krynentechnology/sr2cb/rtl/sr2cb_s_tb.sv

/**
 *  Copyright (C) 2024, Kees Krijnen.
 *
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
 *  License: GPL, v3, as defined and found on www.gnu.org,
 *           https://www.gnu.org/licenses/gpl-3.0.html
 *
 *  Description:
 *
 *  Documents the SR2CB specification by simulation of the SR2CB protocol. The
 *  simulation is setup by SR2CB ring slave nodes clockwise and counterclockwise
 *  byte transfers initiated by a simulated master node (test bench).
 */

`resetall
`timescale 1ns / 1ps
`default_nettype none

// Dependencies:
// `include "../sr2cb_m_phy_pre.v"
// `include "../sr2cb_s.v"
`include "sr2cb_def.v"

/*============================================================================*/
module sr2cb_s_tb;
/*============================================================================*/
localparam NR_CHANNELS = 4;
localparam CHW = $clog2( NR_CHANNELS );

reg        clk = 0;
reg        rst_n = 0;
wire       rx0m_clk;
wire [7:0] rx0m_d;
wire       rx0m_dv;
wire       rx1m_clk;
wire [7:0] rx1m_d;
wire       rx1m_dv;
reg        tx0m_clk = 0;
reg  [7:0] tx0m_d = 0;
reg        tx0m_dv = 0;
wire [7:0] phy_pre_0_d;
wire       phy_pre_0_dv;
wire       phy_pre_0_dr;
reg        tx1m_clk = 0;
reg  [7:0] tx1m_d = 0;
reg        tx1m_dv = 0;
wire [7:0] phy_pre_1_d;
wire       phy_pre_1_dv;
wire       phy_pre_1_dr;
wire [7:0] tx0s0_d;
wire       tx0s0_dv;
wire       tx1s0_clk;
wire [7:0] tx1s0_d;
wire       tx1s0_dv;
wire       tx0s1_clk;
wire [7:0] tx0s1_d;
wire       tx0s1_dv;
wire       tx1s1_clk;
wire [7:0] tx1s1_d;
wire       tx1s1_dv;
wire       tx0s2_clk;
wire [7:0] tx0s2_d;
wire       tx0s2_dv;
wire [7:0] tx1s2_d;
wire       tx1s2_dv;
/*-------------------*/
wire [7:0] rx0s0_ch_d;
wire       rx0s0_ch_dv;
wire       rx0s0_ch_dr;
wire [7:0] tx0s0_ch_d;
wire [CHW-1:0] rx0s0_tx0_ch;
reg  [7:0] rx1s0_ch_d = 0;
reg        rx1s0_ch_dv = 0;
wire       rx1s0_ch_dr;
wire [7:0] tx1s0_ch_d;
wire [CHW-1:0] rx1s0_tx1_ch;
reg  [7:0] rx0s2_ch_d = 0;
reg        rx0s2_ch_dv = 0;
wire       rx0s2_ch_dr;
wire [7:0] tx0s2_ch_d;
wire [CHW-1:0] rx0s2_tx0_ch;
wire [7:0] rx1s2_ch_d;
wire       rx1s2_ch_dv;
wire       rx1s2_ch_dr;
wire [7:0] tx1s2_ch_d;
wire [CHW-1:0] rx1s2_tx1_ch;
/*---------------------------*/
reg   [7:0] rx0_d_count = 0;
reg   [7:0] rx1_d_count = 0;
wire [67:0] rx0s0_rt_clk_count;
wire [67:0] rx1s0_rt_clk_count;
wire [67:0] rx0s1_rt_clk_count;
wire [67:0] rx1s1_rt_clk_count;
wire [67:0] rx0s2_rt_clk_count;
wire [67:0] rx1s2_rt_clk_count;
/*---------------------------*/
reg [7:0] tx0p_d = 0;
reg       tx0p_dv = 0;
reg [7:0] tx0m_d_i = 0;
reg       tx0m_dv_i = 0;
reg [7:0] tx0m_d_ii = 0;
reg       tx0m_dv_ii = 0;
/*---------------------------*/
reg [7:0] tx0s1_d_i = 0;
reg       tx0s1_dv_i = 0;
/*---------------------------*/
reg [7:0] tx0s2_d_i = 0;
reg       tx0s2_dv_i = 0;
/*---------------------------*/
reg [7:0] tx1p_d = 0;
reg       tx1p_dv = 0;
reg [7:0] tx1m_d_i = 0;
reg       tx1m_dv_i = 0;
reg [7:0] tx1m_d_ii = 0;
reg       tx1m_dv_ii = 0;

/*=============================================================================/
RING         | SLV0    |  | SLV1    |         | SLV8190 |  | SLV8191 |
|  +------+  +---------+  +---------+         +---------+  +---------+  +------+
|  |MASTER|  | NP 8191 |  | NP 8190 |         | NP 1    |  | NP 0    |  |MASTER|
CCW|  RX0 |<-| TX0 RX1 |<-| TX0 RX1 |<- - - <-| TX0 RX1 |<-| TX0 RX1 |<-| TX1  |
|  |      |  | NP 0    |    NP 1    |         | NP 8190 |    NP 8191 |  |      |
CW |  TX0 |->| RX0 TX1 |->| RX0 TX1 |->- - ->-| RX0 TX1 |->| RX0 TX1 |->| RX1  |
   +------+  +---------+  +---------+         +---------+  +---------+  +------+
/=============================================================================*/

/*============================================================================*/
sr2cb_m_phy_pre phy_pre_0(
/*============================================================================*/
    .clk(tx0m_clk),
    .rst_n(rst_n),
    .rx_d(tx0m_d),
    .rx_dv(tx0m_dv),
    .rx_dr(phy_pre_0_dr),
    .tx_d(phy_pre_0_d),
    .tx_dv(phy_pre_0_dv)
);

/*============================================================================*/
sr2cb_s slv_node_0(
/*============================================================================*/
    .clk(clk),
    .rst_n(rst_n),
    .rx0_clk(tx0m_clk),
    .rx0_d(tx0m_d_ii),
    .rx0_dv(tx0m_dv_ii),
    .rx0_err(1'b0),
    .tx0_clk(rx0m_clk),
    .tx0_d(tx0s0_d),
    .tx0_dv(tx0s0_dv),
    .tx0_dr(1'b1),
    .tx0_err(),
    .rx1_clk(tx0s1_clk),
    .rx1_d(tx0s1_d_i),
    .rx1_dv(tx0s1_dv_i),
    .rx1_err(1'b0),
    .tx1_clk(tx1s0_clk),
    .tx1_d(tx1s0_d),
    .tx1_dv(tx1s0_dv),
    .tx1_dr(1'b1),
    .tx1_err(),
    .rx0_ch_d(rx0s0_ch_d),
    .rx0_ch_dv(rx0s0_ch_dv),
    .rx0_ch_dr(rx0s0_ch_dr),
    .tx0_ch_d(tx0s0_ch_d),
    .rx0_tx0_ch(rx0s0_tx0_ch),
    .rx1_ch_d(rx1s0_ch_d),
    .rx1_ch_dv(rx1s0_ch_dv),
    .rx1_ch_dr(rx1s0_ch_dr),
    .tx1_ch_d(tx1s0_ch_d),
    .rx1_tx1_ch(rx1s0_tx1_ch),
    .rx0_node_pos(),
    .rx0_c_s(),
    .rx0_status(),
    .rx0_delay(),
    .rx0_rt_clk_count(rx0s0_rt_clk_count),
    .rx0_clk_adjust_fast(),
    .rx1_node_pos(),
    .rx1_c_s(),
    .rx1_status(),
    .rx1_delay(),
    .rx1_rt_clk_count(rx1s0_rt_clk_count),
    .rx1_clk_adjust_fast(),
    .clk_en(),
    .dv_en()
);

defparam slv_node_0.NR_CHANNELS = NR_CHANNELS;

/*============================================================================*/
always @( posedge tx0m_clk ) // Two clock cycle interface RX signal delay
/*============================================================================*/
begin
    tx0p_d     <= 0;
    tx0p_dv    <= 0;
    tx0m_d_i   <= 0;
    tx0m_dv_i  <= 0;
    tx0m_d_ii  <= 0;
    tx0m_dv_ii <= 0;
    if ( rst_n ) begin // Extra clock cycle, tx0m_dv starts at negedge!
        tx0m_d_i   <= ( phy_pre_0_d & { 8{ phy_pre_0_dv }} ) | ( tx0p_d & { 8{ tx0p_dv }} );
        tx0m_dv_i  <= phy_pre_0_dv | tx0p_dv;
        tx0m_d_ii  <= tx0m_d_i;
        tx0m_dv_ii <= tx0m_dv_i;
    end
end // tx0m_clk

reg [7:0] tx0s0_d_i = 0;
reg       tx0s0_dv_i = 0;
/*============================================================================*/
always @( posedge rx0m_clk ) // One clock cycle interface RX signal delay
/*============================================================================*/
begin
    tx0s0_d_i  <= 0;
    tx0s0_dv_i <= 0;
    if ( rst_n ) begin
        tx0s0_d_i  <= tx0s0_d;
        tx0s0_dv_i <= tx0s0_dv;
    end
end // rx0m_clk

assign rx0m_d  = tx0s0_d_i;
assign rx0m_dv = tx0s0_dv_i;

reg [7:0] tx1s0_d_i = 0;
reg       tx1s0_dv_i = 0;
/*============================================================================*/
always @( posedge tx1s0_clk ) // One clock cycle interface RX signal delay
/*============================================================================*/
begin
    tx1s0_d_i  <= 0;
    tx1s0_dv_i <= 0;
    if ( rst_n ) begin
        tx1s0_d_i  <= tx1s0_d;
        tx1s0_dv_i <= tx1s0_dv;
    end
end // tx1s0_clk

/*============================================================================*/
sr2cb_s slv_node_1(
/*============================================================================*/
    .clk(clk),
    .rst_n(rst_n),
    .rx0_clk(tx1s0_clk),
    .rx0_d(tx1s0_d_i),
    .rx0_dv(tx1s0_dv_i),
    .rx0_err(1'b0),
    .tx0_clk(tx0s1_clk),
    .tx0_d(tx0s1_d),
    .tx0_dv(tx0s1_dv),
    .tx0_dr(1'b1),
    .tx0_err(),
    .rx1_clk(tx0s2_clk),
    .rx1_d(tx0s2_d_i),
    .rx1_dv(tx0s2_dv_i),
    .rx1_err(1'b0),
    .tx1_clk(tx1s1_clk),
    .tx1_d(tx1s1_d),
    .tx1_dv(tx1s1_dv),
    .tx1_dr(1'b1),
    .tx1_err(),
    .rx0_ch_d(8'd0),
    .rx0_ch_dv(1'b0),
    .rx0_ch_dr(),
    .tx0_ch_d(),
    .rx0_tx0_ch(),
    .rx1_ch_d(8'd0),
    .rx1_ch_dv(1'b0),
    .rx0_ch_dr(),
    .tx1_ch_d(),
    .rx1_tx1_ch(),
    .rx0_node_pos(),
    .rx0_c_s(),
    .rx0_status(),
    .rx0_delay(),
    .rx0_rt_clk_count(rx0s1_rt_clk_count),
    .rx0_clk_adjust_fast(),
    .rx1_node_pos(),
    .rx1_c_s(),
    .rx1_status(),
    .rx1_delay(),
    .rx1_rt_clk_count(rx1s1_rt_clk_count),
    .rx1_clk_adjust_fast()
);

defparam slv_node_1.NR_CHANNELS = NR_CHANNELS;

/*============================================================================*/
always @( posedge tx0s1_clk ) // One clock cycle interface RX signal delay
/*============================================================================*/
begin
    tx0s1_d_i  <= 0;
    tx0s1_dv_i <= 0;
    if ( rst_n ) begin
        tx0s1_d_i  <= tx0s1_d;
        tx0s1_dv_i <= tx0s1_dv;
    end
end // tx0s1_clk

reg [7:0] tx1s1_d_i = 0;
reg       tx1s1_dv_i = 0;
/*============================================================================*/
always @( posedge tx1s1_clk ) // One clock cycle interface RX signal delay
/*============================================================================*/
begin
    tx1s1_d_i  <= 0;
    tx1s1_dv_i <= 0;
    if ( rst_n ) begin
        tx1s1_d_i  <= tx1s1_d;
        tx1s1_dv_i <= tx1s1_dv;
    end
end // tx1s1_clk

/*============================================================================*/
sr2cb_s slv_node_2(
/*============================================================================*/
    .clk(clk),
    .rst_n(rst_n),
    .rx0_clk(tx1s1_clk),
    .rx0_d(tx1s1_d_i),
    .rx0_dv(tx1s1_dv_i),
    .rx0_err(1'b0),
    .tx0_clk(tx0s2_clk),
    .tx0_d(tx0s2_d),
    .tx0_dv(tx0s2_dv),
    .tx0_dr(1'b1),
    .tx0_err(),
    .rx1_clk(tx1m_clk),
    .rx1_d(tx1m_d_ii),
    .rx1_dv(tx1m_dv_ii),
    .rx1_err(1'b0),
    .tx1_clk(rx1m_clk),
    .tx1_d(tx1s2_d),
    .tx1_dv(tx1s2_dv),
    .tx1_dr(1'b1),
    .tx1_err(),
    .rx0_ch_d(rx0s2_ch_d),
    .rx0_ch_dv(rx0s2_ch_dv),
    .rx0_ch_dr(rx0s2_ch_dr),
    .tx0_ch_d(tx0s2_ch_d),
    .rx0_tx0_ch(rx0s2_tx0_ch),
    .rx1_ch_d(rx1s2_ch_d),
    .rx1_ch_dv(rx1s2_ch_dv),
    .rx1_ch_dr(rx1s2_ch_dr),
    .tx1_ch_d(tx1s2_ch_d),
    .rx1_tx1_ch(rx1s2_tx1_ch),
    .rx0_node_pos(),
    .rx0_c_s(),
    .rx0_status(),
    .rx0_delay(),
    .rx0_rt_clk_count(rx0s2_rt_clk_count),
    .rx0_clk_adjust_fast(),
    .rx1_node_pos(),
    .rx1_c_s(),
    .rx1_status(),
    .rx1_delay(),
    .rx1_rt_clk_count(rx1s2_rt_clk_count),
    .rx1_clk_adjust_fast()
);

defparam slv_node_2.NR_CHANNELS = NR_CHANNELS;

/*============================================================================*/
always @( posedge tx0s2_clk ) // One clock cycle interface RX signal delay
/*============================================================================*/
begin
    tx0s2_d_i  <= 0;
    tx0s2_dv_i <= 0;
    if ( rst_n ) begin
        tx0s2_d_i  <= tx0s2_d;
        tx0s2_dv_i <= tx0s2_dv;
    end
end // tx0s2_clk

/*============================================================================*/
always @( posedge tx1m_clk ) // Two clock cycle interface RX signal delay
/*============================================================================*/
begin
    tx1p_d     <= 0;
    tx1p_dv    <= 0;
    tx1m_d_i   <= 0;
    tx1m_dv_i  <= 0;
    tx1m_d_ii  <= 0;
    tx1m_dv_ii <= 0;
    if ( rst_n ) begin // Extra clock cycle, tx1m_dv starts at negedge!
        tx1m_d_i   <= ( phy_pre_1_d & { 8{ phy_pre_1_dv }} ) | ( tx1p_d & { 8{ tx1p_dv }} );
        tx1m_dv_i  <= phy_pre_1_dv | tx1p_dv;
        tx1m_d_ii  <= tx1m_d_i;
        tx1m_dv_ii <= tx1m_dv_i;
    end
end // tx1m_clk

/*============================================================================*/
sr2cb_m_phy_pre phy_pre_1(
/*============================================================================*/
    .clk(tx1m_clk),
    .rst_n(rst_n),
    .rx_d(tx1m_d),
    .rx_dv(tx1m_dv),
    .rx_dr(phy_pre_1_dr),
    .tx_d(phy_pre_1_d),
    .tx_dv(phy_pre_1_dv)
);

reg [7:0] tx1s2_d_i = 0;
reg       tx1s2_dv_i = 0;

/*============================================================================*/
always @( posedge rx1m_clk ) // One clock cycle interface RX signal delay
/*============================================================================*/
begin
    tx1s2_d_i  <= 0;
    tx1s2_dv_i <= 0;
    if ( rst_n ) begin
        tx1s2_d_i  <= tx1s2_d;
        tx1s2_dv_i <= tx1s2_dv;
    end
end // rx1m_clk

assign rx1m_d  = tx1s2_d_i;
assign rx1m_dv = tx1s2_dv_i;

reg [12:0] node_pos[0:1];
reg [12:0] node_pos_rp[0:1]; // The node positions of returned packets

/*============================================================================*/
task send_r0_byte( input [7:0] byte_in, input set_parity );
/*============================================================================*/
begin
    wait ( tx0m_clk ) @( negedge tx0m_clk );
    tx0m_d[6:0] = byte_in[6:0];
    tx0m_d[7]   = set_parity ? ~( ^byte_in[6:0] ) : byte_in[7];
    tx0m_dv = 1;
end
endtask // send_r0_byte

/*============================================================================*/
task send_r1_byte( input [7:0] byte_in, input set_parity );
/*============================================================================*/
begin
    wait ( tx1m_clk ) @( negedge tx1m_clk );
    tx1m_d[6:0] = byte_in[6:0];
    tx1m_d[7]   = set_parity ? ~( ^byte_in[6:0] ) : byte_in[7];
    tx1m_dv = 1;
end
endtask // send_r1_byte

/*============================================================================*/
task send_r0_command( input [12:0] cmd );
/*============================================================================*/
begin
    wait ( phy_pre_0_dr );
    send_r0_byte( {1'b0, node_pos[0][6:0]}, 1 );
    send_r0_byte( {1'b0, `CW_RDIR, node_pos[0][12:7]}, 1 );
    send_r0_byte( {1'b0, cmd[6:0]}, 1 );
    send_r0_byte( {1'b0, 1'b1, cmd[12:7]}, 1 ); // Set command bit
end
endtask // send_r0_command

/*============================================================================*/
task send_r1_command( input [12:0] cmd );
/*============================================================================*/
begin
    wait ( phy_pre_1_dr );
    send_r1_byte( {1'b0, node_pos[1][6:0]}, 1 );
    send_r1_byte( {1'b0, `CCW_RDIR, node_pos[1][12:7]}, 1 );
    send_r1_byte( {1'b0, cmd[6:0]}, 1 );
    send_r1_byte( {1'b0, 1'b1, cmd[12:7]}, 1 ); // Set command bit
end
endtask // send_r1_command

/*============================================================================*/
task send_r0_status( input [12:0] status );
/*============================================================================*/
begin
    wait ( phy_pre_0_dr );
    send_r0_byte( {1'b0, node_pos[0][6:0]}, 1 );
    send_r0_byte( {1'b0, `CW_RDIR, node_pos[0][12:7]}, 1 );
    send_r0_byte( {1'b0, status[6:0]}, 1 );
    send_r0_byte( {1'b0, 1'b0, status[12:7]}, 1 ); // Reset status bit
end
endtask // send_r0_status

/*============================================================================*/
task send_r1_status( input [12:0] status );
/*============================================================================*/
begin
    wait ( phy_pre_1_dr );
    send_r1_byte( {1'b0, node_pos[1][6:0]}, 1 );
    send_r1_byte( {1'b0, `CCW_RDIR, node_pos[1][12:7]}, 1 );
    send_r1_byte( {1'b0, status[6:0]}, 1 );
    send_r1_byte( {1'b0, 1'b0, status[12:7]}, 1 ); // Reset status bit
end
endtask // send_r1_status

reg [27:0] delay_m[0:1]; // Delay measured by master node
reg [10:0] delay_count = 0;
reg        delay_count_en = 0;
reg [27:0] delay[0:2][0:1]; // Delay received from all nodes
reg        wait_for_rx0m_dv = 0;
reg        wait_for_rx1m_dv = 0;
reg [63:0] master_clk_count = 0;

integer k;
/*============================================================================*/
task send_r0_delay;
/*============================================================================*/
begin
    send_r0_byte( {1'b0, delay_m[0][6:0]}, 1 );
    send_r0_byte( {1'b0, delay_m[0][13:7]}, 1 );
    send_r0_byte( {1'b0, delay_m[0][20:14]}, 1 );
    send_r0_byte( {1'b0, delay_m[0][27:21]}, 1 );
    wait ( tx0m_clk ) @( negedge tx0m_clk );
    tx0m_dv = 0;
    wait ( tx0m_clk ) @( negedge tx0m_clk );
    wait ( ~rx0m_dv ); // Wait for received message has ended!
    wait ( tx0m_clk ) @( negedge tx0m_clk );
    // Wait for rx0m_dv high with time-out
    for ( k = 0; (( k < 1000 ) && wait_for_rx0m_dv ); k = k + 1 ) begin
        #1; // 1ns
    end
    if ( wait_for_rx0m_dv ) begin
        $display( "No messages received from R0 node" );
        $finish;
    end
end
endtask // send_r0_delay

/*============================================================================*/
task send_r1_delay;
/*============================================================================*/
begin
    send_r1_byte( {1'b0, delay_m[1][6:0]}, 1 );
    send_r1_byte( {1'b0, delay_m[1][13:7]}, 1 );
    send_r1_byte( {1'b0, delay_m[1][20:14]}, 1 );
    send_r1_byte( {1'b0, delay_m[1][27:21]}, 1 );
    wait ( tx1m_clk ) @( negedge tx1m_clk );
    tx1m_dv = 0;
    wait ( tx1m_clk ) @( negedge tx1m_clk );
    wait ( ~rx1m_dv ); // Wait for received message has ended!
    wait ( tx1m_clk ) @( negedge tx1m_clk );
    // Wait for rx10m_dv high with time-out
    for ( k = 0; (( k < 1000 ) && wait_for_rx1m_dv ); k = k + 1 ) begin
        #1; // 1ns
    end
    if ( wait_for_rx1m_dv ) begin
        $display( "No messages received from R1 node" );
        $finish;
    end
end
endtask // send_r1_delay

reg [7:0]  rx0_d_c;
reg [1:0]  rx0_dv_i = 0;
reg [2:0]  rx0_status = `eR_IDLE;
reg [13:0] rx0_c_s = 0;
reg [3:0]  rx0_nb_bytes = 0;
reg [5:0]  rx0_nb_samples = 0;
reg        rx0_loopback = 0;
wire       rx0_nb_samples_c;
wire       rx0_clk_sync_c_s;
wire       rx0_clk_sync_cmd;
wire       rx0_clk_sync_st;
wire       rx0_clk_sync_set_cmd;
assign rx0_nb_samples_c = ( 2 << ( rx0_c_s & 13'h3 )) == rx0_nb_samples;
assign rx0_clk_sync_c_s = ( `CLK_SYNC_0 >> 3 ) == rx0_c_s[12:3];
assign rx0_clk_sync_cmd = rx0_clk_sync_c_s & rx0_c_s[13];
assign rx0_clk_sync_st = rx0_clk_sync_c_s & !rx0_c_s[13] & !rx0_c_s[2];
assign rx0_clk_sync_set_cmd = rx0_clk_sync_c_s & rx0_c_s[13] & rx0_c_s[2];
assign rx0s0_ch_dv = rx0s0_ch_dr && ( 0 == rx0s0_tx0_ch );
assign rx0s0_ch_d = rx0_d_count;

reg [7:0]  rx1_d_c;
reg [1:0]  rx1_dv_i = 0;
reg [2:0]  rx1_status = `eR_IDLE;
reg [13:0] rx1_c_s = 0;
reg [3:0]  rx1_nb_bytes = 0;
reg [5:0]  rx1_nb_samples = 0;
reg        rx1_loopback = 0;
wire       rx1_nb_samples_c;
wire       rx1_clk_sync_c_s;
wire       rx1_clk_sync_cmd;
wire       rx1_clk_sync_st;
wire       rx1_clk_sync_set_cmd;
assign rx1_nb_samples_c = ( 2 << ( rx1_c_s & 13'h3 )) == rx1_nb_samples;
assign rx1_clk_sync_c_s = ( `CLK_SYNC_0 >> 3 ) == rx1_c_s[12:3];
assign rx1_clk_sync_cmd = rx1_clk_sync_c_s && rx1_c_s[13];
assign rx1_clk_sync_st = rx1_clk_sync_c_s && !rx1_c_s[13] && !rx1_c_s[2];
assign rx1_clk_sync_set_cmd = rx1_clk_sync_c_s && rx1_c_s[13] && rx1_c_s[2];
assign rx1s2_ch_dv = rx1s2_ch_dr && ( 3 == rx1s2_tx1_ch );
assign rx1s2_ch_d = rx1_d_count;

/*============================================================================*/
task send_r0_clock_sync( input [12:0] cmd );
/*============================================================================*/
begin
    rx0_status   = `eR_INIT;
    rx1_status   = `eR_IDLE;
    rx0_loopback = 0;
    rx1_loopback = 1;
    if (( cmd & 13'h1FFC ) != `CLK_SYNC_0 ) begin
        $display( "Incorrect clock sync command!" );
        $stop;
    end
    node_pos[0] = 0;
    delay_count = 0;
    repeat ( 1 << cmd[1:0]) begin
        send_r0_command( cmd );
        send_r0_delay;
        wait ( ~rx0m_dv ); // Wait for received message has ended!
        wait ( tx0m_clk ) @( negedge tx0m_clk );
    end
    if ( !delay_m[0] ) begin
        delay_m[0] = { {9{1'b0}},  {{delay_count, 4'h0} >> ( cmd[1:0] + 1 ) }};
    end
    cmd = cmd | 13'h4; // Set delay valid bit "_SET"
    send_r0_command( cmd );
    send_r0_delay;
    wait ( ~rx0m_dv ); // Wait for received message has ended!
    wait ( tx0m_clk ) @( negedge tx0m_clk );
end
endtask // send_r0_clock_sync

/*============================================================================*/
task send_r1_clock_sync( input [12:0] cmd );
/*============================================================================*/
begin
    rx0_status   = `eR_IDLE;
    rx1_status   = `eR_INIT;
    rx0_loopback = 1;
    rx1_loopback = 0;
    if (( cmd & 13'h1FFC ) != `CLK_SYNC_0 ) begin
        $display( "Incorrect clock sync command!" );
        $stop;
    end
    node_pos[1] = 0;
    delay_count = 0;
    repeat ( 1 << cmd[1:0]) begin
        send_r1_command( cmd );
        send_r1_delay;
        wait ( ~rx1m_dv ); // Wait for received message has ended!
        wait ( tx1m_clk ) @( negedge tx1m_clk );
    end
    if ( !delay_m[1] ) begin
        delay_m[1] = { {9{1'b0}},  {{delay_count, 4'h0} >> ( cmd[1:0] + 1 ) }};
    end
    cmd = cmd | 13'h4; // Set delay valid bit "_SET"
    send_r1_command( cmd );
    send_r1_delay;
    wait ( ~rx1m_dv ); // Wait for received message has ended!
    wait ( tx1m_clk ) @( negedge tx1m_clk );
end
endtask // send_r1_clock_sync

integer m = 0;
/*============================================================================*/
task send_r0_packet( input [13:0] c_s );
/*============================================================================*/
begin
    wait ( phy_pre_0_dr );
    if ( c_s[13] ) begin
        send_r0_command( c_s[12:0] );
    end
    else begin
        if ( 0 == c_s[12:10] ) begin // Send master clock status
            send_r0_status( {3'd0, master_clk_count[9:0]} );
        end
        else begin
            send_r0_status( c_s[12:0] );
        end
    end
    for ( m = 0; m < NR_CHANNELS; m = m + 1 ) begin
        send_r0_byte( 0, 0 );
    end
    wait ( tx0m_clk ) @( negedge tx0m_clk );
    tx0m_dv = 0;
    wait ( tx0m_clk ) @( negedge tx0m_clk );
end
endtask // send_r0_packet

integer n = 0;
/*============================================================================*/
task send_r1_packet( input [13:0] c_s );
/*============================================================================*/
begin
    wait ( phy_pre_1_dr );
    if ( c_s[13] ) begin
        send_r1_command( c_s[12:0] );
    end
    else begin
        if ( 0 == c_s[12:10] ) begin // Send master clock status
            send_r1_status( {3'd0, master_clk_count[9:0]} );
        end
        else begin
            send_r1_status( c_s[12:0] );
        end
    end
    for ( n = 0; n < NR_CHANNELS; n = n + 1 ) begin
        send_r1_byte( 0, 0 );
    end
    wait ( tx1m_clk ) @( negedge tx1m_clk );
    tx1m_dv = 0;
    wait ( tx1m_clk ) @( negedge tx1m_clk );
end
endtask // send_r1_packet

localparam NODE_POS_OFFSET = 8; // PREAMBLE_SFD for phy_pre_0/1

/*============================================================================*/
always @( posedge rx0m_clk ) begin : rx0_process
/*============================================================================*/
    tx0p_d  <= 0;
    tx0p_dv <= 0;
    if (( `eR_IDLE == rx0_status ) && rx0_loopback ) begin
        tx0p_d  <= rx0m_d;
        tx0p_dv <= rx0m_dv;
    end

    rx0_dv_i <= { rx0_dv_i[0], rx0m_dv };

    if ( rx0m_dv ) begin
        if ( NODE_POS_OFFSET == rx0_nb_bytes ) begin
            node_pos_rp[0][6:0] <= rx0m_d[6:0];
            if ( `eR_IDLE == rx0_status ) begin
                tx0p_d[6:0] <= 0; // Set node position to zero
                tx0p_d[7]   <= 1;
            end
        end
        if (( NODE_POS_OFFSET + 1 ) == rx0_nb_bytes ) begin
            node_pos_rp[0][12:7] <= rx0m_d[5:0];
            if ( `eR_IDLE == rx0_status ) begin
                tx0p_d[6:0] <= 0; // Set node position to zero
                tx0p_d[7]   <= 1;
            end
        end
        if (( NODE_POS_OFFSET + 2 ) == rx0_nb_bytes ) begin
            rx0_c_s[6:0] <= rx0m_d[6:0];
            if ( `eR_IDLE == rx0_status ) begin
                if (( `CLK_SYNC_SET_0 >> 2 ) == rx0m_d[6:2] ) begin // Check for CLK_SYNC_SET cmd
                    tx0p_d[6:0] <= 0; // NOP command
                    tx0p_d[7]   <= 1;
                end
            end
        end
        if (( NODE_POS_OFFSET + 3 ) == rx0_nb_bytes ) begin
            rx0_c_s[13:7] <= rx0m_d[6:0];
            rx0_d_c = { rx0m_d[7], 1'b0, rx0m_d[5:0] };
            if ( `eR_IDLE == rx0_status ) begin
                tx0p_d[6:0] <= rx0_d_c; // NOP command bit
                tx0p_d[7]   <= ~( ^rx0_d_c ); // Set even partity
                if ( !tx0p_d[6:0] ) begin // Check for NOP cmd
                    tx0p_d[5:0] <= 0;     // NOP command
                    tx0p_d[7:6] <= 2'b01; // Set command bit + parity
                end
            end
        end
        if (( NODE_POS_OFFSET + 4 ) == rx0_nb_bytes ) begin
            if (( `CLK_SYNC_SET_0 >> 2 ) == rx0_c_s[12:2] ) begin
                if ( 0 == node_pos_rp[0] ) begin
                    delay[0][0][6:0] <= rx0m_d[6:0];
                end
                if ( 1 == node_pos_rp[0] ) begin
                    delay[1][0][6:0] <= rx0m_d[6:0];
                end
                if ( 2 == node_pos_rp[0] ) begin
                    delay[2][0][6:0] <= rx0m_d[6:0];
                end
            end
            if ( !rx0_nb_samples_c ) begin
                rx0_nb_samples <= rx0_nb_samples + 1;
            end
        end
        if (( NODE_POS_OFFSET + 5 ) == rx0_nb_bytes ) begin
            if (( `CLK_SYNC_SET_0 >> 2 ) == rx0_c_s[12:2] ) begin
                if ( 0 == node_pos_rp[0] ) begin
                    delay[0][0][13:7] <= rx0m_d[6:0];
                end
                if ( 1 == node_pos_rp[0] ) begin
                    delay[1][0][13:7] <= rx0m_d[6:0];
                end
                if ( 2 == node_pos_rp[0] ) begin
                    delay[2][0][13:7] <= rx0m_d[6:0];
                end
            end
        end
        if (( NODE_POS_OFFSET + 6 ) == rx0_nb_bytes ) begin
            if (( `CLK_SYNC_SET_0 >> 2 ) == rx0_c_s[12:2] ) begin
                if ( 0 == node_pos_rp[0] ) begin
                    delay[0][0][20:14] <= rx0m_d[6:0];
                end
                if ( 1 == node_pos_rp[0] ) begin
                    delay[1][0][20:14] <= rx0m_d[6:0];
                end
                if ( 2 == node_pos_rp[0] ) begin
                    delay[2][0][20:14] <= rx0m_d[6:0];
                end
            end
        end
        if (( NODE_POS_OFFSET + 7 ) == rx0_nb_bytes ) begin
            if (( `CLK_SYNC_SET_0 >> 2 ) == rx0_c_s[12:2] ) begin
                if ( 0 == node_pos_rp[0] ) begin
                    delay[0][0][27:21] <= rx0m_d[6:0];
                end
                if ( 1 == node_pos_rp[0] ) begin
                    delay[1][0][27:21] <= rx0m_d[6:0];
                end
                if ( 2 == node_pos_rp[0] ) begin
                    delay[2][0][27:21] <= rx0m_d[6:0];
                end
            end
        end
        rx0_nb_bytes = rx0_nb_bytes + 1;
    end
    else begin
        rx0_nb_bytes = 0;
        if (( `CLK_SYNC_SET_0 >> 2 ) == rx0_c_s[12:2] ) begin
            if ( rx0_nb_samples_c ) begin
                rx0_nb_samples <= 0;
            end
        end
    end

    if ( rx0s0_ch_dv ) begin
        rx0_d_count <= rx0_d_count + 1;
    end
end // rx0_process

/*============================================================================*/
always @( posedge rx1m_clk ) begin : rx1_process
/*============================================================================*/
    tx1p_d  <= 0;
    tx1p_dv <= 0;
    if (( `eR_IDLE == rx1_status ) && rx1_loopback ) begin
        tx1p_d  <= rx1m_d;
        tx1p_dv <= rx1m_dv;
    end

    rx1_dv_i <= { rx1_dv_i[0], rx1m_dv };

    if ( rx1m_dv ) begin
        if ( NODE_POS_OFFSET == rx1_nb_bytes ) begin
            node_pos_rp[1][6:0] <= rx1m_d[6:0];
            if ( `eR_IDLE == rx1_status ) begin
                tx1p_d[6:0] <= 0; // Set node position to zero
                tx1p_d[7]   <= 1;
            end
        end
        if (( NODE_POS_OFFSET + 1 ) == rx1_nb_bytes ) begin
            node_pos_rp[1][12:7] <= rx1m_d[5:0];
            if ( `eR_IDLE == rx1_status ) begin
                tx1p_d[6:0] <= 0; // Set node position to zero
                tx1p_d[7]   <= 1;
            end
        end
        if (( NODE_POS_OFFSET + 2 ) == rx1_nb_bytes ) begin
            rx1_c_s[6:0] <= rx1m_d[6:0];
            if ( `eR_IDLE == rx1_status ) begin
                if (( `CLK_SYNC_SET_0 >> 2 ) == rx1m_d[6:2] ) begin // Check for CLK_SYNC_SET cmd
                    tx1p_d[6:0] <= 0; // NOP command
                    tx1p_d[7]   <= 1;
                end
            end
        end
        if (( NODE_POS_OFFSET + 3 ) == rx1_nb_bytes ) begin
            rx1_c_s[13:7] <= rx1m_d[6:0];
            rx1_d_c = { rx1m_d[7], 1'b0, rx1m_d[5:0] };
            if ( `eR_IDLE == rx1_status ) begin
                tx1p_d[6:0] <= rx1_d_c; // NOP command bit
                tx1p_d[7]   <= ~( ^rx1_d_c ); // Set even partity
                if ( !tx1p_d[6:0] ) begin // Check for NOP cmd
                    tx1p_d[5:0] <= 0;     // NOP command
                    tx1p_d[7:6] <= 2'b01; // Set command bit + parity
                end
            end
        end
        if (( NODE_POS_OFFSET + 4 ) == rx1_nb_bytes ) begin
            if (( `CLK_SYNC_SET_0 >> 2 ) == rx1_c_s[12:2] ) begin
                if ( 0 == node_pos_rp[1] ) begin
                    delay[0][1][6:0] <= rx1m_d[6:0];
                end
                if ( 1 == node_pos_rp[1] ) begin
                    delay[1][1][6:0] <= rx1m_d[6:0];
                end
                if ( 2 == node_pos_rp[1] ) begin
                    delay[2][1][6:0] <= rx1m_d[6:0];
                end
            end
            if ( !rx1_nb_samples_c ) begin
                rx1_nb_samples <= rx1_nb_samples + 1;
            end
        end
        if (( NODE_POS_OFFSET + 5 ) == rx1_nb_bytes ) begin
            if (( `CLK_SYNC_SET_0 >> 2 ) == rx1_c_s[12:2] ) begin
                if ( 0 == node_pos_rp[1] ) begin
                    delay[0][1][13:7] <= rx1m_d[6:0];
                end
                if ( 1 == node_pos_rp[1] ) begin
                    delay[1][1][13:7] <= rx1m_d[6:0];
                end
                if ( 2 == node_pos_rp[1] ) begin
                    delay[2][1][13:7] <= rx1m_d[6:0];
                end
            end
        end
        if (( NODE_POS_OFFSET + 6 ) == rx1_nb_bytes ) begin
            if (( `CLK_SYNC_SET_0 >> 2 ) == rx1_c_s[12:2] ) begin
                if ( 0 == node_pos_rp[1] ) begin
                    delay[0][1][20:14] <= rx1m_d[6:0];
                end
                if ( 1 == node_pos_rp[1] ) begin
                    delay[1][1][20:14] <= rx1m_d[6:0];
                end
                if ( 2 == node_pos_rp[1] ) begin
                    delay[2][1][20:14] <= rx1m_d[6:0];
                end
            end
        end
        if (( NODE_POS_OFFSET + 7 ) == rx1_nb_bytes ) begin
            if (( `CLK_SYNC_SET_0 >> 2 ) == rx1_c_s[12:2] ) begin
                if ( 0 == node_pos_rp[1] ) begin
                    delay[0][1][27:21] <= rx1m_d[6:0];
                end
                if ( 1 == node_pos_rp[1] ) begin
                    delay[1][1][27:21] <= rx1m_d[6:0];
                end
                if ( 2 == node_pos_rp[1] ) begin
                    delay[2][1][27:21] <= rx1m_d[6:0];
                end
            end
        end
        rx1_nb_bytes = rx1_nb_bytes + 1;
    end
    else begin
        rx1_nb_bytes = 0;
        if (( `CLK_SYNC_SET_0 >> 2 ) == rx1_c_s[12:2] ) begin
            if ( rx1_nb_samples_c ) begin
                rx1_nb_samples <= 0;
            end
        end
    end

    if ( rx1s2_ch_dv ) begin
        rx1_d_count <= rx1_d_count + 1;
    end
end // rx1_process

reg [1:0]  rx0m_clk_i = 0;
reg [1:0]  rx1m_clk_i = 0;
reg [1:0]  tx0m_clk_i = 0;
reg [1:0]  tx1m_clk_i = 0;
/*--------------------------*/
reg rx0m_dv_posedge = 0;
reg tx0m_dv_posedge = 0;
reg rx1m_dv_posedge = 0;
reg tx1m_dv_posedge = 0;

/*============================================================================*/
always @( posedge clk ) begin : handle_ports
/*============================================================================*/
    rx0m_clk_i <= { rx0m_clk_i[0], rx0m_clk };
    rx1m_clk_i <= { rx1m_clk_i[0], rx1m_clk };
    tx0m_clk_i <= { tx0m_clk_i[0], tx0m_clk };
    tx1m_clk_i <= { tx1m_clk_i[0], tx1m_clk };

    rx0m_dv_posedge <= ( 2'b01 == rx0m_clk_i ) && rx0m_dv;
    tx0m_dv_posedge <= ( 2'b01 == tx0m_clk_i ) && tx0m_dv;
    rx1m_dv_posedge <= ( 2'b01 == rx1m_clk_i ) && rx1m_dv;
    tx1m_dv_posedge <= ( 2'b01 == tx1m_clk_i ) && tx1m_dv;

    if ( `eR_INIT == rx0_status ) begin
        if ( tx0m_dv_posedge && !rx0m_dv ) begin
            delay_count_en <= !delay_m[0]; // Start counting when delay has not been set yet
        end

        if ( rx0m_dv_posedge ) begin
            delay_count_en <= 0;
        end
    end

    if ( tx0m_dv && !tx0m_dv_i ) begin
        wait_for_rx0m_dv <= 1;
    end

    if ( rx0m_dv_posedge ) begin
        wait_for_rx0m_dv <= 0;
    end

    if ( `eR_INIT == rx1_status ) begin
        if ( tx1m_dv_posedge && !rx1m_dv ) begin
            delay_count_en <= !delay_m[1]; // Start counting when delay has not been set yet
        end

        if ( rx1m_dv_posedge ) begin
            delay_count_en <= 0;
        end
    end

    if ( tx1m_dv && !tx1m_dv_i ) begin
        wait_for_rx1m_dv <= 1;
    end

    if ( rx1m_dv_posedge ) begin
        wait_for_rx1m_dv <= 0;
    end

    if ( delay_count_en ) begin
        delay_count <= delay_count + 1;
    end

    master_clk_count <= master_clk_count + 1;
end // handle_ports

always #5  clk = ~clk; // 100 MHz clock
always #40 tx0m_clk = ~tx0m_clk; // 12.5 MHz clock
always #40 tx1m_clk = ~tx1m_clk; // 12.5 MHz clock

localparam [12:0] CLK_SYNC_CMD = `CLK_SYNC_0; // Select *_0, *_1, *_2 or *_3!
localparam [12:0] CLK_SYNC_CMD_SET = CLK_SYNC_CMD | 13'h4;

reg [9:0] rx0_mclk_count = 0;
reg [9:0] rx1_mclk_count = 0;
reg passed = 0;
integer i = 0;
integer j = 0;
/*============================================================================*/
task ring_init;
/*============================================================================*/
begin
    send_r0_clock_sync( CLK_SYNC_CMD );
    // Resend CLK_SYNC_SET_0 command, wait for delay[2][0] set!
    for ( i = 0; (( i < 10 ) && !delay[2][0] ); i = i + 1 ) begin
        send_r0_command( CLK_SYNC_CMD_SET );
        send_r0_delay;
    end
    rx0_status = `eR_IDLE;

    $display( "delay[0][0] = %0d.%0d, slv_node_0 rx0_status = %0d",
        delay[0][0][27:4], delay[0][0][3:0], slv_node_0.rx0_status );
    $display( "delay[1][0] = %0d.%0d, slv_node_1 rx0_status = %0d",
        delay[1][0][27:4], delay[1][0][3:0], slv_node_1.rx0_status );
    $display( "delay[2][0] = %0d.%0d, slv_node_2 rx0_status = %0d",
        delay[2][0][27:4], delay[2][0][3:0], slv_node_2.rx0_status );
    passed = ( delay[0][0] > 0 ) && ( delay[1][0] > 0 ) && ( delay[2][0] > 0 ) &&
        ( 3 == slv_node_0.rx0_status) && ( 3 == slv_node_1.rx0_status) && ( 3 == slv_node_2.rx0_status);
    $display( "Initialization R0 %s", ( passed ? "passed" : "failed" ));

    if ( !delay[2][0] ) begin
        $display( "No delay[2][0] value received via R0 node" );
        $finish;
    end

    // Flush all messages from ring!
    for ( i = 0; ( i < delay[2][0] ); i = i + 1 ) begin
        #5; // 5ns
    end

    wait ( !rx1_dv_i );

    send_r1_clock_sync( CLK_SYNC_CMD );
    // Resend CLK_SYNC_SET_0 command, wait for delay[2][1] set!
    for ( i = 0; (( i < 10 ) && !delay[2][1] ); i = i + 1 ) begin
        send_r1_command( CLK_SYNC_CMD_SET );
        send_r1_delay;
    end

    wait ( !rx0_dv_i );

    rx0_loopback = 0;
    rx1_loopback = 0;
    rx1_status   = `eR_IDLE;

    #1000;
    $display( "" );
    $display( "delay[2][1] = %0d.%0d, slv_node_0 rx0_status = %0d rx1_status = %0d",
        delay[2][1][27:4], delay[2][1][3:0], slv_node_0.rx0_status, slv_node_0.rx1_status );
    $display( "delay[1][1] = %0d.%0d, slv_node_1 rx0_status = %0d rx1_status = %0d",
        delay[1][1][27:4], delay[1][1][3:0], slv_node_1.rx0_status, slv_node_1.rx1_status );
    $display( "delay[0][1] = %0d.%0d, slv_node_2 rx0_status = %0d rx1_status = %0d",
        delay[0][1][27:4], delay[0][1][3:0], slv_node_2.rx0_status, slv_node_2.rx1_status );
    passed = ( delay[0][1] > 0 ) && ( delay[1][1] > 0 ) && ( delay[2][1] > 0 ) &&
        ( 4 == slv_node_0.rx0_status) && ( 4 == slv_node_1.rx0_status) && ( 4 == slv_node_2.rx0_status) &&
        ( 4 == slv_node_0.rx1_status) && ( 4 == slv_node_1.rx1_status) && ( 4 == slv_node_2.rx1_status);
    $display( "Initialization R0 and R1 %s", ( passed ? "passed" : "failed" ));
    $display( "" );

    if ( !delay[2][1] ) begin
        $display( "No delay[2][1] value received via R1 node" );
        $finish;
    end

    $display( "Master, clock R0/R1 = %0d before clock reset", master_clk_count );
    $display( "Slave node 0, clock R0 = %0d.%0d, clock R1 = %0d.%0d",
        slv_node_0.rx0_clk_count[67:4], slv_node_0.rx0_clk_count[3:0],
        slv_node_0.rx1_clk_count[67:4], slv_node_0.rx1_clk_count[3:0] );
    $display( "Slave node 1, clock R0 = %0d.%0d, clock R1 = %0d.%0d",
        slv_node_1.rx0_clk_count[67:4], slv_node_1.rx0_clk_count[3:0],
        slv_node_1.rx1_clk_count[67:4], slv_node_1.rx1_clk_count[3:0] );
    $display( "Slave node 2, clock R0 = %0d.%0d, clock R1 = %0d.%0d",
        slv_node_2.rx0_clk_count[67:4], slv_node_2.rx0_clk_count[3:0],
        slv_node_2.rx1_clk_count[67:4], slv_node_2.rx1_clk_count[3:0] );
    $display( "" );

    master_clk_count = 0;
    fork // Parallel operation
        send_r0_packet( {1'b1, `CLK_RESET} );
        send_r1_packet( {1'b1, `CLK_RESET} );
    join
    wait ( rx0m_dv );
    wait ( rx1m_dv );
    #1000; // 1us

    rx0_mclk_count = ( master_clk_count[9:0] - 20 );
    send_r0_packet( `MASTER_CLK_10L | rx0_mclk_count ); // Master clock status
    rx1_mclk_count = ( master_clk_count[9:0] + 20 );
    send_r1_packet( `MASTER_CLK_10L | rx1_mclk_count );

    #1000; // 1us

    $display( "M/S clocks reset, set slave nodes rx0/rx1 clocks with +/-200ns!" );
    $display( "Slave node 0, clock R0 = %0d.%0d, M0 = %0d, clock R1 = %0d.%0d, M1 = %0d",
        slv_node_0.rx0_clk_count[67:4], slv_node_0.rx0_clk_count[3:0], slv_node_0.rx0_mclk_count,
        slv_node_0.rx1_clk_count[67:4], slv_node_0.rx1_clk_count[3:0], slv_node_0.rx1_mclk_count );
    $display( "Slave node 1, clock R0 = %0d.%0d, M0 = %0d, clock R1 = %0d.%0d, M1 = %0d",
        slv_node_1.rx0_clk_count[67:4], slv_node_1.rx0_clk_count[3:0], slv_node_1.rx0_mclk_count,
        slv_node_1.rx1_clk_count[67:4], slv_node_1.rx1_clk_count[3:0], slv_node_1.rx1_mclk_count );
    $display( "Slave node 2, clock R0 = %0d.%0d, M0 = %0d, clock R1 = %0d.%0d, M1 = %0d",
        slv_node_2.rx0_clk_count[67:4], slv_node_2.rx0_clk_count[3:0], slv_node_2.rx0_mclk_count,
        slv_node_2.rx1_clk_count[67:4], slv_node_2.rx1_clk_count[3:0], slv_node_2.rx1_mclk_count );
    $display( "" );

    passed = 0;
    for ( i = 0; (( i < 200 ) && !passed ); i = i + 1 ) begin
        fork // Parallel operation
            send_r0_packet( {1'b1, `CMD_NOP} );
            send_r1_packet( {1'b1, `CMD_NOP} );
        join
        passed = ( 0 == slv_node_0.rx0_mclk_delta ) && ( 0 == slv_node_0.rx1_mclk_delta ) &&
            ( 0 == slv_node_1.rx0_mclk_delta ) && ( 0 == slv_node_1.rx1_mclk_delta ) &&
            ( 0 == slv_node_2.rx0_mclk_delta ) && ( 0 == slv_node_2.rx1_mclk_delta );
    end

    $display( "Slave node 0, clock R0 = %0d -> %0d, clock R1 = %0d -> %0d", rx0s0_rt_clk_count[67:4], master_clk_count,
        rx1s0_rt_clk_count[67:4], master_clk_count );
    $display( "Slave node 1, clock R0 = %0d -> %0d, clock R1 = %0d -> %0d", rx0s1_rt_clk_count[67:4], master_clk_count,
        rx1s1_rt_clk_count[67:4], master_clk_count );
    $display( "Slave node 2, clock R0 = %0d -> %0d, clock R1 = %0d -> %0d", rx0s2_rt_clk_count[67:4], master_clk_count,
        rx1s2_rt_clk_count[67:4], master_clk_count );
    $display( "Clock synchronization R0 and R1 %s", ( passed ? "passed" : "failed" ));
    $display( "" );

    $display( "Master, clock R0/R1 = %0d", master_clk_count );
    $display( "Slave node 0, RT clock R0 = %0d.%0d, RT clock R1 = %0d.%0d", rx0s0_rt_clk_count[67:4], rx0s0_rt_clk_count[3:0],
        rx1s0_rt_clk_count[67:4], rx1s0_rt_clk_count[3:0] );
    $display( "Slave node 1, RT clock R0 = %0d.%0d, RT clock R1 = %0d.%0d", rx0s1_rt_clk_count[67:4], rx0s1_rt_clk_count[3:0],
        rx1s1_rt_clk_count[67:4], rx1s1_rt_clk_count[3:0] );
    $display( "Slave node 2, RT clock R0 = %0d.%0d, RT clock R1 = %0d.%0d", rx0s2_rt_clk_count[67:4], rx0s2_rt_clk_count[3:0],
        rx1s2_rt_clk_count[67:4], rx1s2_rt_clk_count[3:0] );
    $display( "" );
end
endtask // ring_init

/*============================================================================*/
initial begin // Test bench
/*============================================================================*/
    rst_n  = 0;
    clk    = 0;
    passed = 0;
    /*---------*/
    for ( j = 0; j < 3; j = j + 1 ) begin
        for ( i = 0; i < 2; i = i + 1 ) delay[j][i] = 0;
    end
    for ( i = 0; i < 2; i = i + 1 ) begin
        delay_m[i]        = 0;
        node_pos[i]       = 0;
        node_pos_rp[i]    = 0;
    end
    #100    // 100ns
    $display( "SR2CB slave simulation started" );
    rst_n = 1;
    #100    // 100ns
    ring_init;
    #10000  // 10us
    $finish;
end

/*============================================================================*/
initial begin // Generate VCD file for GTKwave
/*============================================================================*/
`ifdef GTK_WAVE
    $dumpfile( "sr2cb_s_tb.vcd" );
    $dumpvars( 0 );
`endif
end

endmodule // sr2cb_s_tb
